wavius/Subsystem-A-ECE295/LTSpice/Subsystem_A.asc

C1: cap; 2.05n
C2: cap; 100n
C3: cap; 100n
C4: cap; 1µ
C5: cap; 100n
C6: cap; 100n
C7: cap; 1µ
C8: cap; 100n
C9: cap; 1n
C10: cap; 390p
C11: cap; 100p
C12: cap; 390p
C13: cap; 1n
C14: cap; 1n
C15: cap; 1µ
C16: cap; 100n
C17: cap; 100n
C18: cap; 100n
C19: cap; 100n
C20: cap; 100n
C21: cap; 2.05n
C25: cap; 1n
C26: cap; 100n
C27: cap; 100n
C28: cap; 100n
C29: cap; 100n
C30: cap; 100n
C31: cap; 100n
C32: cap; 100n
C33: cap; 100n
C34: cap; 100n
C35: cap; 1µ
C37: cap; 1µ
C38: cap; 1µ
C39: cap; 1n
C40: cap; 1n
L1: ind; 10µ
L2: ind; 10µ
L3: ind; 10µ
L4: ind; 10µ
L5: ind; 10µ
L6: ind; 10µ
L7: ind; 560n; Rser=1m
L8: ind; 2µ; Rser=1m
L9: ind; 560n; Rser=1m
L10: ind; 10µ
L11: ind; 10µ
L12: ind; 10µ
L13: ind; 10µ
L14: ind; 10µ
L15: ind; 10µ
M1: nmos; Si7336ADP
Q1: npn; M_BFR93A
Q2: npn; M_BFR93A
Q3: npn; M_BFR93A
Q4: npn; M_BFR93A
Q5: npn; M_BFR93A
Q6: npn; M_BFR93A
Q7: npn; M_BFR93A
Q8: npn; M_BFR93A
Q9: npn; M_BFR93A
Q10: npn; M_BFR93A
Q11: npn; M_BFR93A
Q12: npn; M_BFR93A
Q13: npn; M_BFR93A
Q14: npn; M_BFR93A
Q15: npn; M_BFR93A
Q16: npn; M_BFR93A
Q17: npn; M_BFR93A
Q18: npn; M_BFR93A
R1: res; 2k
R2: res; 2k
R3: res; 100
R4: res; 100k
R5: res; 3.3k
R6: res; 3.3k
R7: res; 100
R8: res; 100k
R9: res; 3.3k
R10: res; 100k
R11: res; 2k
R12: res; 100k
R13: res; 3.3k
R14: res; 500
R15: res; 300
R16: res; 300
R17: res; 300
R18: res; 200
R20: res; 300
R21: res; 10k
R22: res; 50
R23: res; 1k
R24: res; 1k
R25: res; 1.43k
R26: res; 1.02k
R27: res; 10k
R28: res; 50
R29: res; 2k
R30: res; 2k
R31: res; 10k
R32: res; 3.3k
R33: res; 3.3k
R34: res; 10k
R40: res; 3.3k
R44: res; 1k
R45: res; 1k
R46: res; 10k
R48: res; 2k
R49: res; 100
R51: res; 1.43k
R52: res; 5k
R53: res; 5k
R54: res; 500
R55: res; 33
R56: res; 1.02k
R57: res; 200
R64: res; 300
R65: res; 300
R66: res; 100k
R67: res; 100k
R68: res; 100k
R69: res; 100k
R73: res; 100
R75: res; 3.3k
R88: res; 1k
R89: res; 1k
R90: res; 30k
R91: res; 1k
R92: res; 10k
R93: res; 10k
R96: res; 50
U1: ADA4807
U2: ADA4807
U3: ADA4807
U4: ADA4807
U5: ADA4807
U6: ADA4807
V1: voltage; PULSE(0 3.3 10u 1n 1n 0.5 1)
V2: voltage; 5
VI: voltage; ""; AC 1; Rser=0 Cpar=0
VIN: voltage; SINE(0 0.01 12.05Meg); Rser=0 Cpar=0
VLO1: voltage; SINE(1.65 1.65 12Meg 41.666n 0)
VLO3: voltage; SINE(1.65 1.65 12Meg 0 0)
Named nets: V+, 0, VLNA, VI, VOUT1, VBP, VB1, VB2, ENABLE, VOUT2
.tran 0 150u 0
.ac dec 60 1 100Meg
K1 L1 L2 L3 1
K2 L4 L5 L6 1
.MODEL M_BFR93A NPN(TNOM=25 IS=6.872E-016 BF=134 NF=0.9872 VAF=30.8 IKF=0.3501 ISE=6.927E-016 NE=1.61 BR=22.18 NR=0.987 VAR=2.847 IKR=0.1135 ISC=1.465E-014 NC=2.001 RB=9.292 IRB=0.0001166 RBM=0.85 RE=0.34281 RC=1.266 XTB=1.303 EG=1.11 XTI=6.548 CJE=2.029E-012 VJE=0.9052 MJE=0.4406 TF=2.248E-011 XTF=146.1 VTF=8 ITF=2.097 PTF=1E-015 CJC=5.99092E-013 VJC=0.554562 MJC=0.359703 XCJC=0.1048 TR=5.53E-009 CJS=0 MJS=0 VJS=0.75 FC=0.9999 KF=0 AF=1)
.op
.noise V(VLNA) VIN dec 60 1 20Meg
K4 L10 L11 L12 1
K3 L13 L14 L15 1
